akomakom/esp32-deathwatch/main/us.h

#ifndef US_H_
#define US_H_

#define US_ECHO_PIN CONFIG_US_ECHO_PIN
#define US_TRIG_PIN CONFIG_US_TRIG_PIN

#define US_READ_DELAY 10000

// Number of reading DELAYS (US_READ_DELAY) that must elapse before we stop trusting
// the old distance reading if we can't get a good one.
#define US_MAX_READING_AGE 5

#define US_BAD_READING -1
// reject all readings if among the US_NUM_READINGS readings (max-min)/max is greater than this
#define US_MAX_DEVIATION 0.4
// how many successive readings to average
#define US_NUM_READINGS 5

void initialize_ultrasound(void (*callback)(double));

#endif
